BoujeeEnjinia1701/lampnode/cad/drawings/LPN-DWG-001.pdf

CONCEPT, NOT FOR FABRICATION | LampNode · github.com/BoujeeEnjinia1701/lampnode

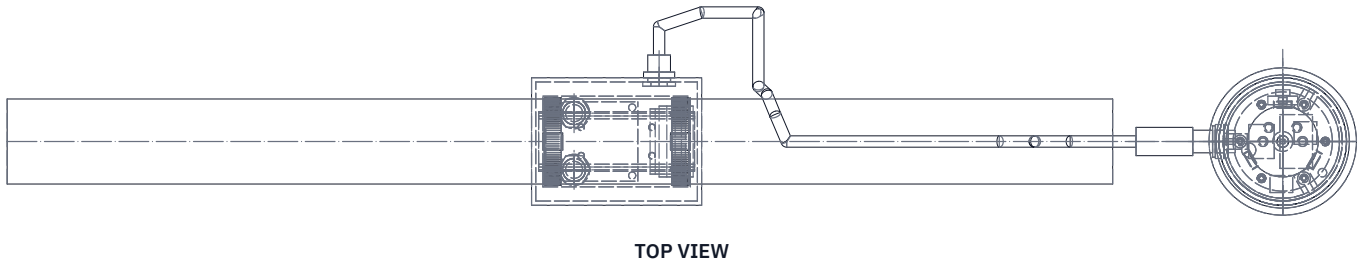
[picture p3: figure]
TOP VIEW
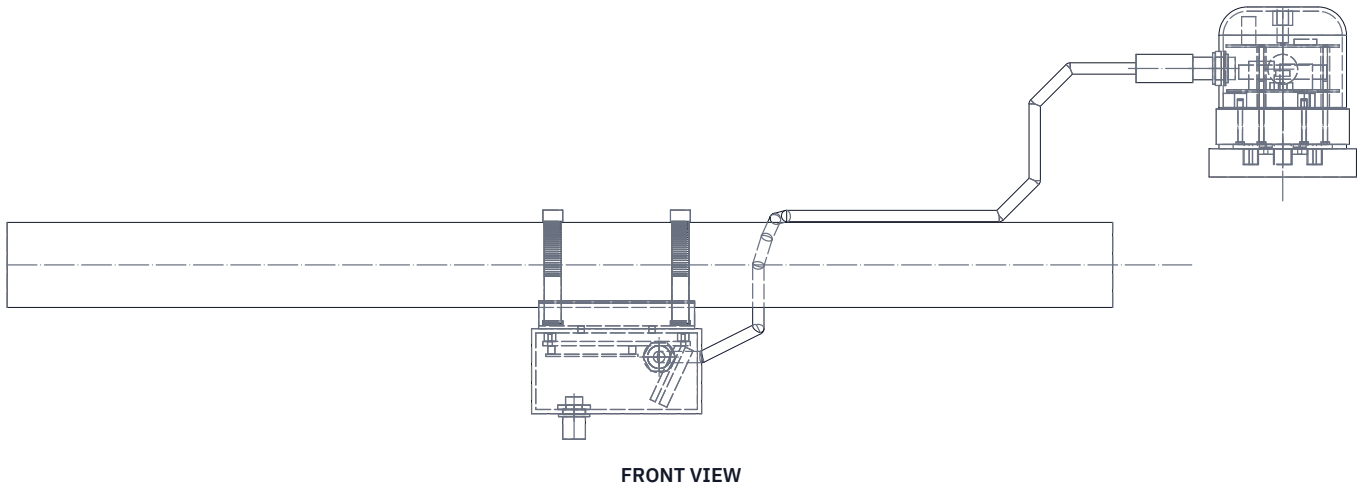
[picture p4: figure]
FRONT VIEW

Scale 1:5; looking at the front (along +Y)

Scale 1:5; looking down (along -Z)

RIGHT VIEW
Scale 1:5; looking at the right side (along -X)

952

147 305

ISOMETRIC VIEW
Not to scale; grey = existing receptacle and arm; seen from the front right and above, about 30 deg elevation

KEY DIMENSIONS AND INTERFACES (MM)
Controller 94 dia. x 111 incl. blades; dome 90 x 72
Base: ANSI C136.41 7-contact twist-lock (representative), 3 power blades, 4 low-voltage contacts, no earth
Sensor head 120 x 90 x 60, center 470 from
receptacle toward the pole; 15 below a 60 dia. arm
Radar tilted 25 deg down, looking along the street
M12 5-pole: dome pad to head, 1 m cable; 2 ports in head lid Band clamps for 50 to 80 arms, pitch 90, through
slots in a folded 2 mm bracket; arm rests on rubber strips
Dome and board stack: 6 x M3 from under the base
Mains 120 to 277 V AC; 0 to 10 V dimming; relay normally closed Ports 12 V SELV, 3 W total; 2.5 W above 50 C inside
US915 radio; port pins 1 12 V, 3 gnd, 2 and 4 RS-485, 5 wake Mass: controller 0.33 kg, head 0.42 kg (LPN-CAL-001) PRELIMINARY, NOT FOR FABRICATION
REV | DESCRIPTION | DATE | BY
P1 | Preliminary GA from cad/src/model.py (LPN-CAL-001) | 2026-09-25 | AC
P2 | Port power note: 2.5 W above 50 C inside (LPN-DDR-002) | 2026-09-25 | AC
P3 | Design for construction: fixings, boards, bracket (LPN-DDR-003) | 2026-09-30 | AC
P4 | Decisions of 2026-10-02: 915 MHz radio band and the M12 port pinout added to the notes | 2026-10-02 | AC
LAMPNODE | github.com/BoujeeEnjinia1701/lampnode

## General arrangement, controller and sensor head

DRAWING NO.
LPN-DWG-001

REV
P4

SHEET
1 of 1

SIZE

## ANSI B

SCALE
1:5

UNITS
mm
PROJECTION | DATE
2026-10-02

DRAWN
Amish Chadha

MATERIAL / NOTES
Dome ASA; base and head box PC; clamps stainless; bracket 2 mm Al. See bom/bom.csv
Licensed CERN-OHL-S-2.0 · Design Molecule Lab · designmolecule.com | Generated from cad/src; do not edit by hand
