BoujeeEnjinia1701/lampnode/cad/drawings/LPN-DWG-106.pdf

### BUILD PLAN SKETCH, PLAN NOT YET BUILT LampNode · github.com/BoujeeEnjinia1701/lampnode

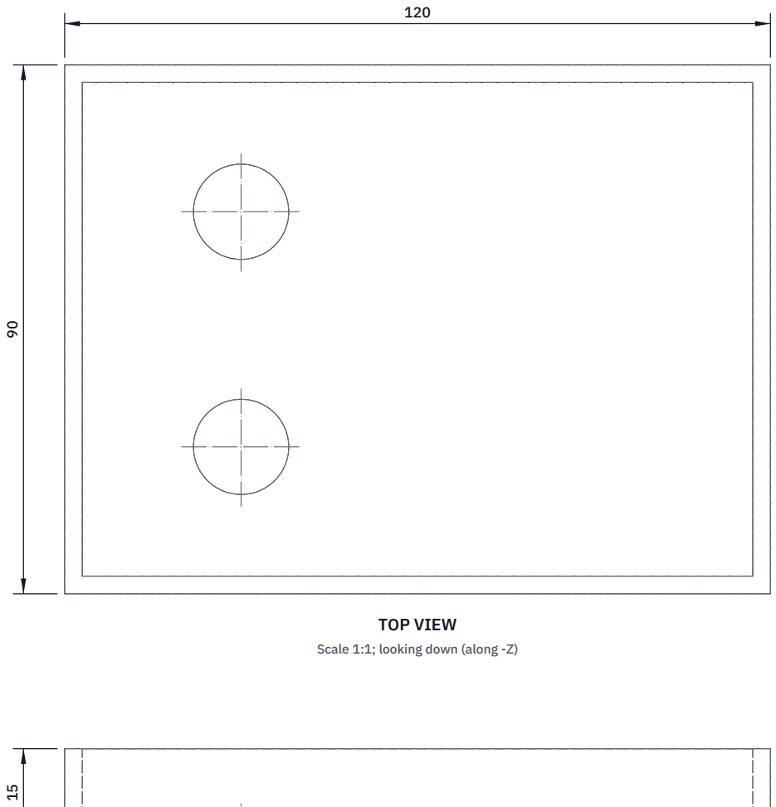
[picture p5: figure]
TOP VIEW; Scale 1:1; looking down (along -Z)

FRONT VIEW
Scale 1:1; looking at the front (along +Y)

RIGHT VIEW
Scale 1:1; looking at the right side (along -X)

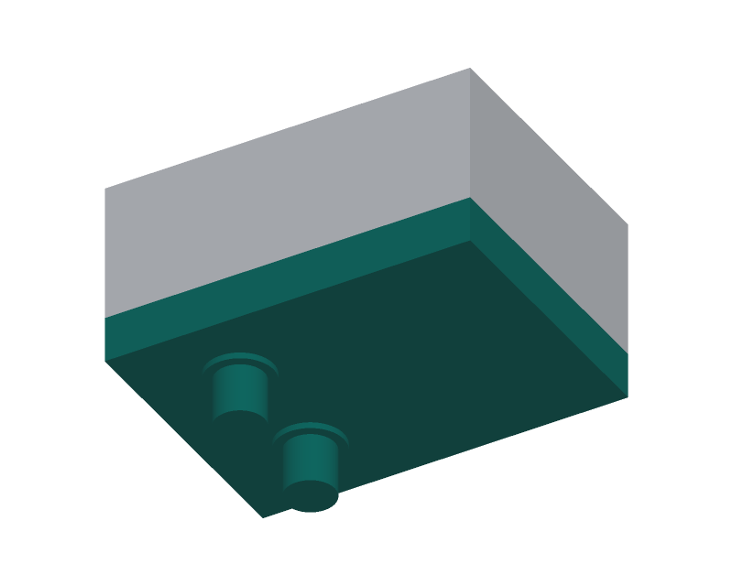
[picture p6: figure]

WHERE IT GOES
This part in colour, its neighbours in grey

HOW TO MAKE IT AND HOW IT FITS
The lid is 15 mm deep and faces the street below.
Two 16.2 mm holes for the M12 expansion ports, 30 mm toward the pole end from the middle, 20 mm each side of the centre line (40 apart). Drill as for the box: tape, 3 mm pilot, step drill, deburr.
Fit each port from outside with its seal, nut inside, maker's torque. Solder a 150 mm lead set to each port and fit a plug-in connector,
so the lid can come off without a soldering iron.
Wire each port to the pinout proposed to FieldNode: pin 1 12 V supply, pin 3 ground, pins 2 and 4 the RS-485 pair, pin 5 wake line.
Check: each port seats flat on its seal; the lid gasket is unbroken.
REV | DESCRIPTION | DATE | BY
P1 | Making sketch for the prototype build plan | 2026-09-30 | AC
P2 | M12 pin numbers added to the notes (decision of 2026-10-02) | 2026-10-02 | AC
LAMPNODE | github.com/BoujeeEnjinia1701/lampnode

## LampNode sensor head lid (bought): drilling sketch

DRAWING NO.
LPN-DWG-106

REV
P2

SHEET
1 of 1

SIZE

## ANSI B

SCALE
1:1

UNITS
mm
PROJECTION | DATE
2026-10-02

DRAWN
Amish Chadha

MATERIAL / NOTES
Lid of the bought IP66 box, polycarbonate
Licensed CERN-OHL-S-2.0 · Design Molecule Lab · designmolecule.com | Generated from cad/src; do not edit by hand
