BoujeeEnjinia1701/lampnode/cad/drawings/LPN-DWG-107.pdf

### BUILD PLAN SKETCH, PLAN NOT YET BUILT LampNode · github.com/BoujeeEnjinia1701/lampnode

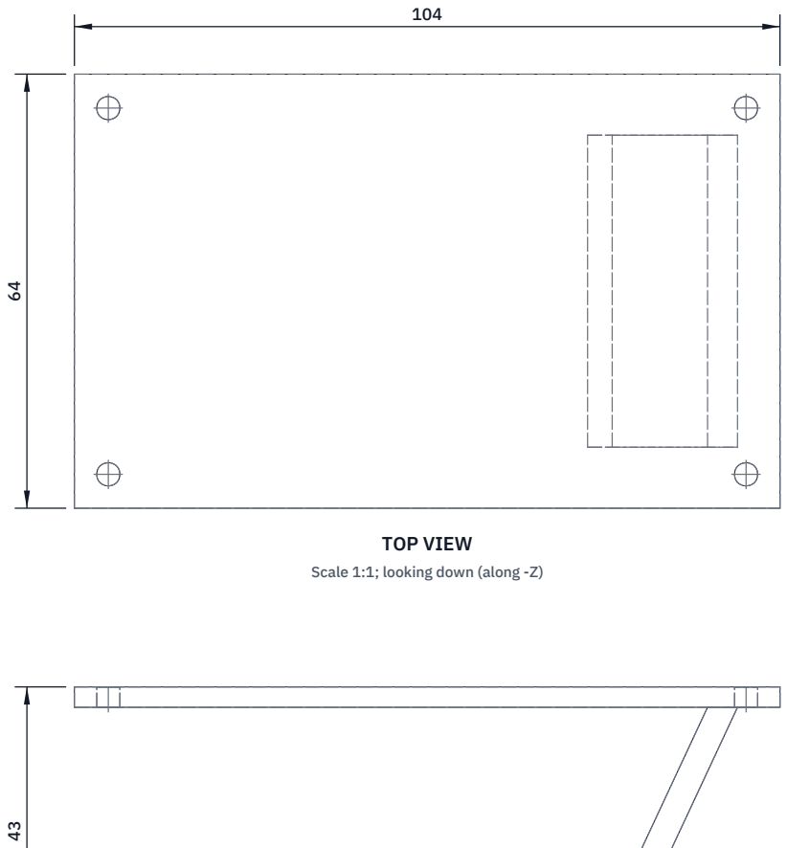
[picture p7: figure]
TOP VIEW; Scale 1:1; looking down (along -Z)

FRONT VIEW
Scale 1:1; looking at the front (along +Y)

RIGHT VIEW
Scale 1:1; looking at the right side (along -X)

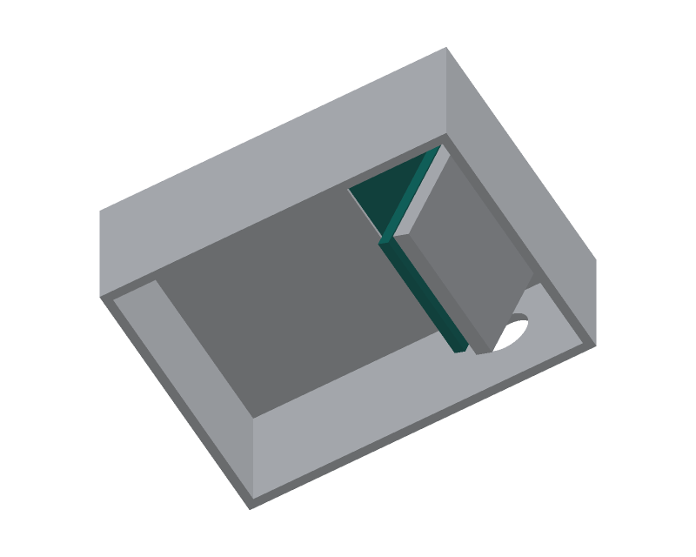
[picture p8: figure]

WHERE IT GOES
This part in colour, its neighbours in grey

HOW TO MAKE IT AND HOW IT FITS
One print: a plate 104 x 64 x 3 mm and a cradle 4 mm thick, 46 mm wide, 44 mm long, hanging below the street end at 25 degrees from upright. Print with the plate flat on the bed and the cradle overhanging.
Four 3.4 mm holes 94 mm apart along and 54 mm apart across, to match the four bosses in the box (measure your box first).
Cradle: two 2.7 mm holes to match the radar module's mounting holes. The module sits 3 mm off the cradle on nylon spacers.
Head board: four M3 standoffs 6 mm long on the underside,
at the board's corner holes, 4 mm in from each edge.
Head board port outputs follow the M12 pinout: pin 1 12 V, pin 3 ground, pins 2 and 4 RS-485, pin 5 wake; the lead plugs are marked 1 to 5.
Fit: four M3 screws into the bosses from below.
Check: the radar face then tips 25 degrees down toward the street.
REV | DESCRIPTION | DATE | BY
P1 | Making sketch for the prototype build plan | 2026-09-30 | AC
P2 | M12 pin numbers added to the notes (decision of 2026-10-02) | 2026-10-02 | AC
LAMPNODE | github.com/BoujeeEnjinia1701/lampnode

## LampNode head internal plate: making sketch

DRAWING NO.
LPN-DWG-107

REV
P2

SHEET
1 of 1

SIZE

## ANSI B

SCALE
1:1

UNITS
mm
PROJECTION | DATE
2026-10-02

DRAWN
Amish Chadha

MATERIAL / NOTES
ASA, 3D printed, 100 % infill
Licensed CERN-OHL-S-2.0 · Design Molecule Lab · designmolecule.com | Generated from cad/src; do not edit by hand
