BoujeeEnjinia1701/lampnode/cad/drawings/LPN-DWG-101.pdf

### BUILD PLAN SKETCH, PLAN NOT YET BUILT LampNode · github.com/BoujeeEnjinia1701/lampnode

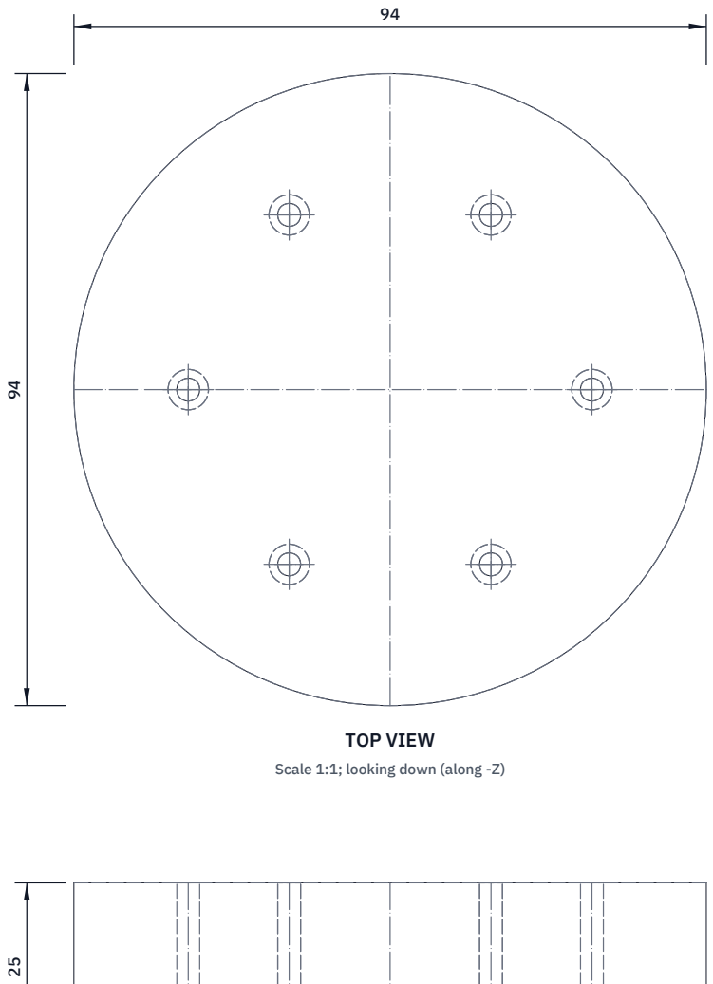
[picture p39: figure]
TOP VIEW; Scale 1:1; looking down (along -Z)

FRONT VIEW
Scale 1:1; looking at the front (along +Y)

RIGHT VIEW
Scale 1:1; looking at the right side (along -X)

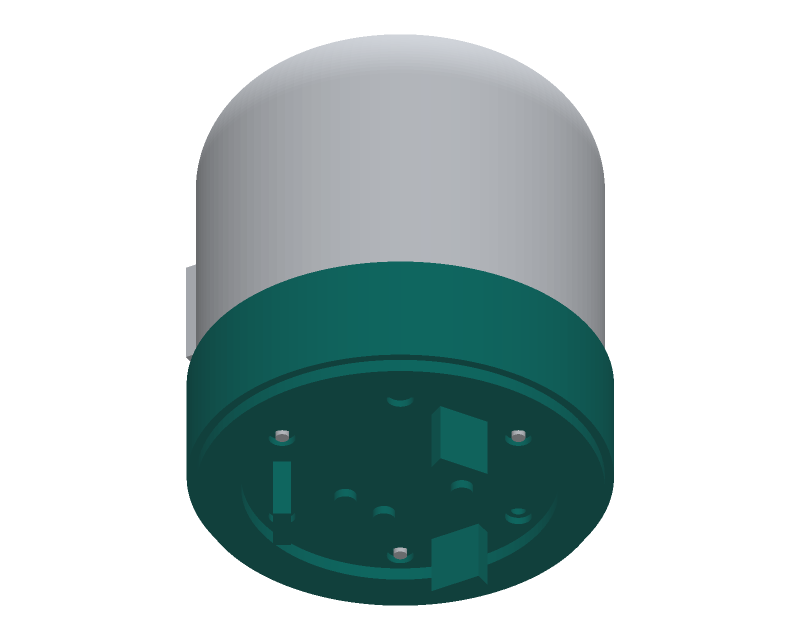
[picture p40: figure]

WHERE IT GOES
This part in colour, its neighbours in grey

HOW TO MAKE IT AND HOW IT FITS
Bought base kit, 94 mm across, 25 mm tall. Drill six holes right through it. All six sit on one 60 mm circle round the centre, between the blades: dome screws at 60, 180 and 300 degrees; stack screws at 0, 120 and 240 degrees, anticlockwise from the street side seen from above.
The base drilling layout picture shows them from below.
Drill 3.4 mm through, with a scrap block under the top face. Countersink each hole from below, 6 mm across, so the screw heads sit flush inside the gasket ring and clear of the contact wells.
Keep the gasket ring (35 to 45 mm radius underneath) untouched. Crimp a 150 mm lead on each blade (1.0 mm2) and each low-voltage contact (0.25 mm2) before anything is fitted on top.
Check: no hole breaks into a blade pocket or the gasket ring.
REV | DESCRIPTION | DATE | BY
P1 | Making sketch for the prototype build plan | 2026-09-30 | AC
LAMPNODE | github.com/BoujeeEnjinia1701/lampnode

## LampNode twist-lock base (bought): drilling sketch

DRAWING NO.
LPN-DWG-101

REV
P1

SHEET
1 of 1

SIZE

## ANSI B

SCALE
1:1

UNITS
mm
PROJECTION | DATE
2026-09-30

DRAWN
Amish Chadha

MATERIAL / NOTES
Bought ANSI C136.41 7-contact base kit, polycarbonate
Licensed CERN-OHL-S-2.0 · Design Molecule Lab · designmolecule.com | Generated from cad/src; do not edit by hand
