BoujeeEnjinia1701/lampnode/cad/drawings/LPN-DWG-102.pdf

### BUILD PLAN SKETCH, PLAN NOT YET BUILT LampNode · github.com/BoujeeEnjinia1701/lampnode

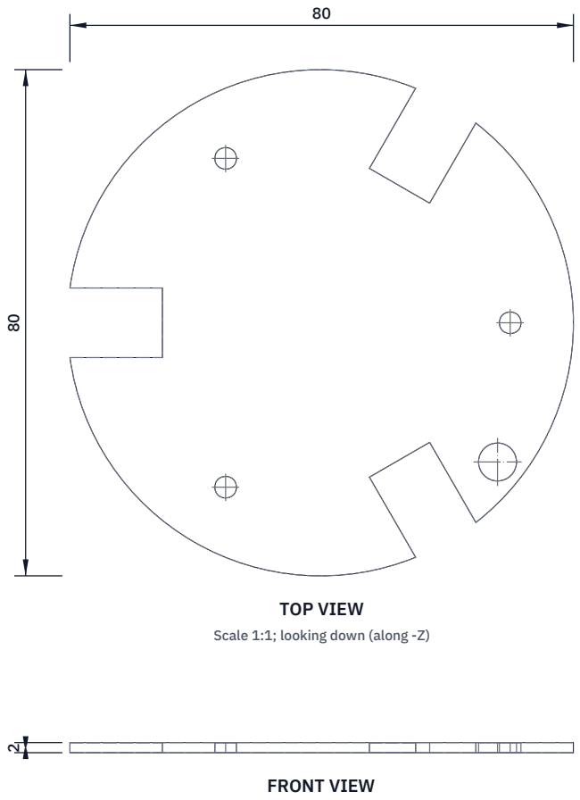
[picture p41: figure]
FRONT VIEW; TOP VIEW; Scale 1:1; looking down (along -Z)

Scale 1:1; looking at the front (along +Y)

RIGHT VIEW
Scale 1:1; looking at the right side (along -X)

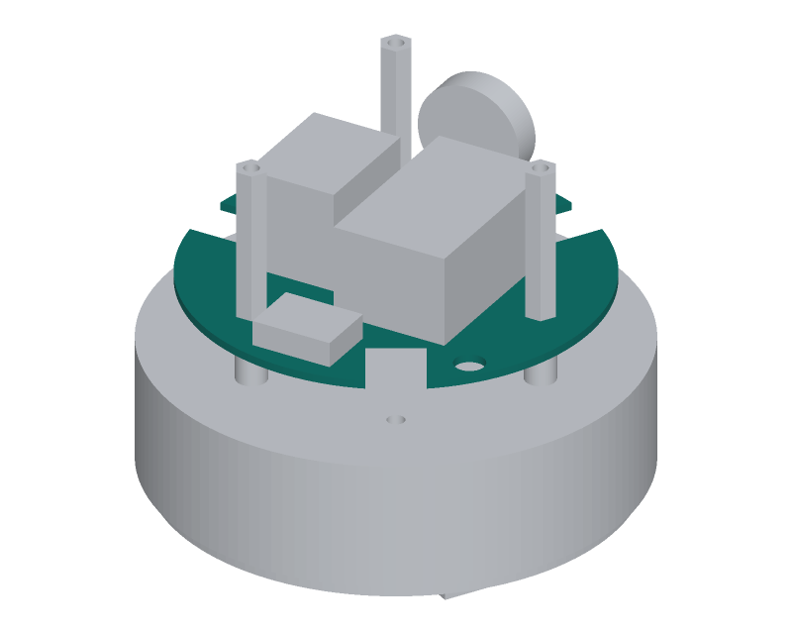
[picture p42: figure]

WHERE IT GOES
This part in colour, its neighbours in grey

HOW TO MAKE IT AND HOW IT FITS
Cut an 80 mm disc from plated-hole prototype board (2.54 mm grid): scribe the circle, cut outside it with a coping saw, file to the line.
Three stack holes 3.4 mm on a 60 mm circle at 0, 120 and 240 degrees. Three notches 11 mm wide, from 25 mm radius out to the edge, at 60, 180 and 300 degrees: the dome bosses pass up through them.
Parts, from the mains board layout picture: supply 23 x 38 mm on the centre; relay on the pole side; varistor and thermal fuse at the left
edge and metering module at the right edge, seen from the pole.
6 mm hole at 28 mm toward the street, 22 mm right: low-voltage leads. Keep 6 mm of bare board between mains tracks and the 12 V side. Fit a 3-way mains terminal block and a 6-way harness header.
Fit: sits on three 12 mm spacers; standoffs screw on top.
Check: flat; the dome bosses pass the notches freely.
REV | DESCRIPTION | DATE | BY
P1 | Making sketch for the prototype build plan | 2026-09-30 | AC
LAMPNODE | github.com/BoujeeEnjinia1701/lampnode

## LampNode mains board: making sketch

DRAWING NO.
LPN-DWG-102

REV
P1

SHEET
1 of 1

SIZE

## ANSI B

SCALE
1:1

UNITS
mm
PROJECTION | DATE
2026-09-30

DRAWN
Amish Chadha

MATERIAL / NOTES
Plated-hole FR4 prototype board 1.6 mm
Licensed CERN-OHL-S-2.0 · Design Molecule Lab · designmolecule.com | Generated from cad/src; do not edit by hand
