BoujeeEnjinia1701/lampnode/cad/drawings/LPN-DWG-103.pdf

### BUILD PLAN SKETCH, PLAN NOT YET BUILT LampNode · github.com/BoujeeEnjinia1701/lampnode

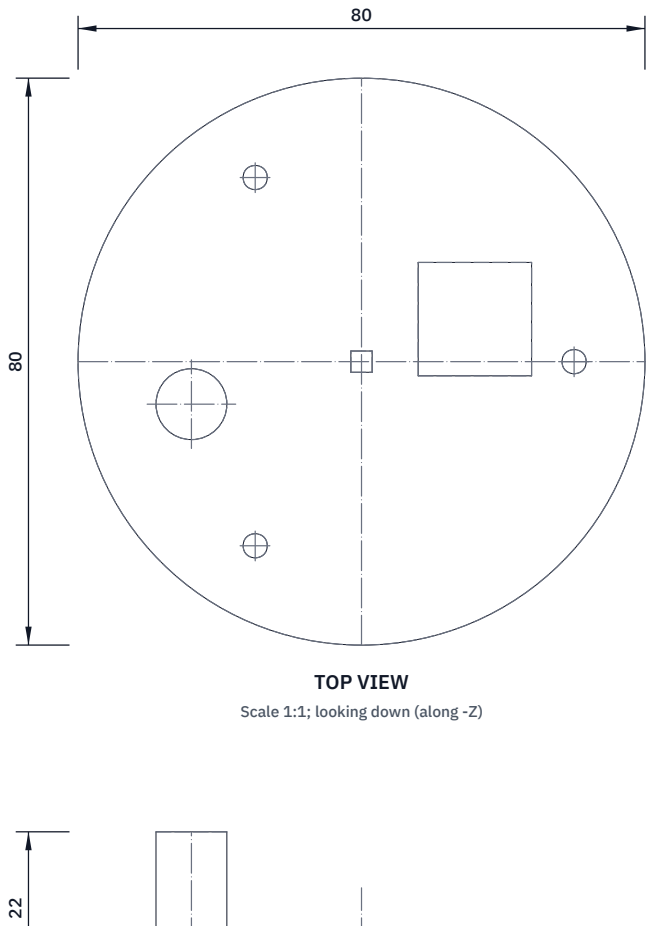
[picture p43: figure]
TOP VIEW; Scale 1:1; looking down (along -Z)

FRONT VIEW
Scale 1:1; looking at the front (along +Y)

RIGHT VIEW
Scale 1:1; looking at the right side (along -X)

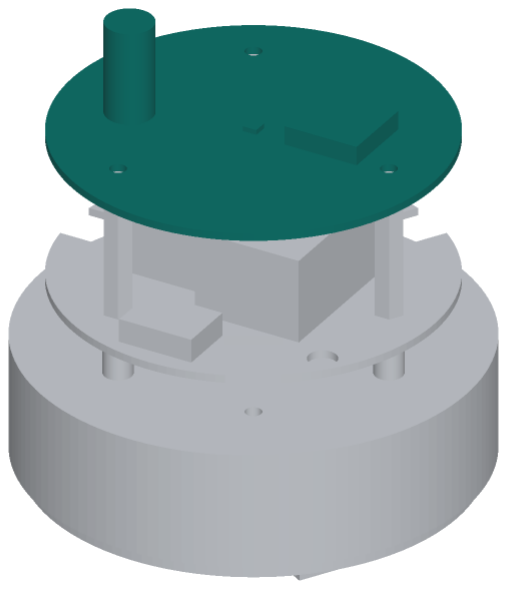
[picture p44: figure]

WHERE IT GOES
This part in colour, its neighbours in grey

HOW TO MAKE IT AND HOW IT FITS
Cut an 80 mm disc as for the mains board; no notches.
Three holes 3.4 mm on a 60 mm circle at 0, 120 and 240 degrees. Light sensor at the exact centre, on the top face; the light pipe
ends 0.5 mm above it once the dome is on.
Radio module breakout 16 x 16 mm on the street side, its u.FL socket toward the right edge (seen from the pole) for the antenna lead. Supercapacitor 10 mm across, 20 mm tall, standing 24 mm toward the pole and 6 mm to the right of the centre, clear of the screw heads.
Clock, accelerometer, 0 to 10 V stage and coil drive on the rest.
Fit: three M3 x 6 screws into the standoffs, top of board 70.2 mm
above the underside of the base.
Check: nothing on the top face stands taller than 22 mm.
REV | DESCRIPTION | DATE | BY
P1 | Making sketch for the prototype build plan | 2026-09-30 | AC
LAMPNODE | github.com/BoujeeEnjinia1701/lampnode

## LampNode controller board: making sketch

DRAWING NO.
LPN-DWG-103

REV
P1

SHEET
1 of 1

SIZE

## ANSI B

SCALE
1:1

UNITS
mm
PROJECTION | DATE
2026-09-30

DRAWN
Amish Chadha

MATERIAL / NOTES
Plated-hole FR4 prototype board 1.6 mm
Licensed CERN-OHL-S-2.0 · Design Molecule Lab · designmolecule.com | Generated from cad/src; do not edit by hand
