BoujeeEnjinia1701/lampnode/cad/drawings/LPN-DWG-104.pdf

### BUILD PLAN SKETCH, PLAN NOT YET BUILT LampNode · github.com/BoujeeEnjinia1701/lampnode

FRONT VIEW
Scale 1:2; looking at the front (along +Y)

TOP VIEW
Scale 1:2; looking down (along -Z)

RIGHT VIEW
Scale 1:2; looking at the right side (along -X)

92

90 71

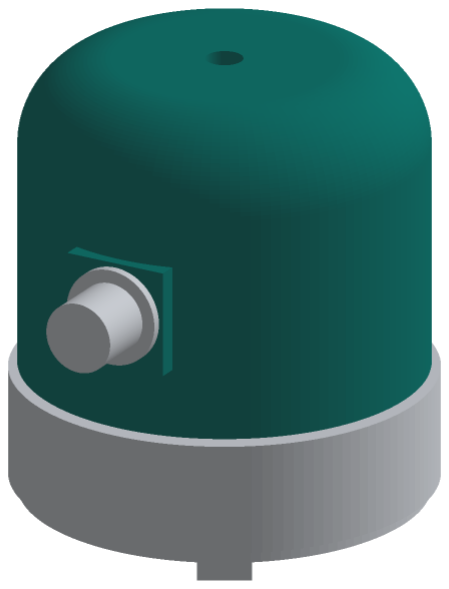
[picture p45: figure]

WHERE IT GOES
This part in colour, its neighbours in grey

HOW TO MAKE IT AND HOW IT FITS
Print upside down on its top, in ASA in an enclosed printer.
Shell 90 mm across, 71 mm tall, 3 mm wall, 20 mm round top edge. Three bosses 9 mm across, 10 mm tall, inside the foot on a 60 mm circle at 60, 180 and 300 degrees, each tied to the wall by a rib. Press an M3 brass heat-set insert into each boss with a soldering iron. Flat pad on the pole side (180 degrees): 24 x 24 mm, 6 mm thick, face 0.5 mm outside the base edge, centre 27.6 mm above the dome foot. 16.2 mm hole through it for the M12 socket.
Light pipe hole 8.2 mm at the top centre, with a 10 mm sleeve inside. Gasket: cut a ring 90 mm outside, 84 mm inside from 1 mm EPDM sheet. Fit: foot on the gasket; three M3 x 30 screws from under the base. Check: the foot sits flat on the base all round, no light under it.
REV | DESCRIPTION | DATE | BY
P1 | Making sketch for the prototype build plan | 2026-09-30 | AC
LAMPNODE | github.com/BoujeeEnjinia1701/lampnode

## LampNode dome: making sketch

DRAWING NO.
LPN-DWG-104

REV
P1

SHEET
1 of 1

SIZE

## ANSI B

SCALE
1:2

UNITS
mm
PROJECTION | DATE
2026-09-30

DRAWN
Amish Chadha

MATERIAL / NOTES
ASA, 3D printed, 4 walls, 40 % infill
Licensed CERN-OHL-S-2.0 · Design Molecule Lab · designmolecule.com | Generated from cad/src; do not edit by hand
