BoujeeEnjinia1701/lampnode/cad/drawings/LPN-DWG-105.pdf

### BUILD PLAN SKETCH, PLAN NOT YET BUILT LampNode · github.com/BoujeeEnjinia1701/lampnode

FRONT VIEW
Scale 1:2; looking at the front (along +Y)

TOP VIEW
Scale 1:2; looking down (along -Z)

RIGHT VIEW
Scale 1:2; looking at the right side (along -X)

120

90 45

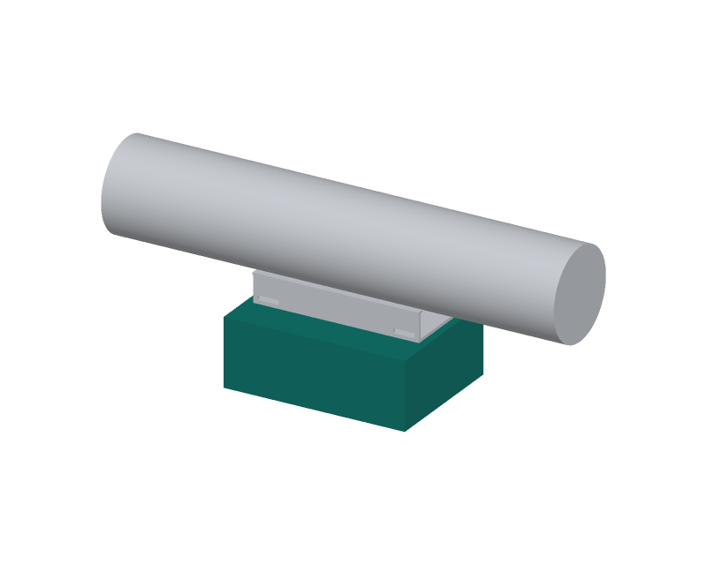
[picture p46: figure]

WHERE IT GOES
This part in colour, its neighbours in grey

HOW TO MAKE IT AND HOW IT FITS
Bought box; its base faces up and its 15 mm lid faces down.
The end wall facing the street end of the arm is the radar window: never drill it, paint it or put a label on it.
Top face: four 4.5 mm holes for the bracket screws, 25 mm each side of the middle along the box and 10 mm each side across it.
Left side wall, seen from the pole: one 16.2 mm hole for the cable gland, 30 mm toward the street end from the middle, 20 mm below the top. Tape the faces, pilot drill 3 mm slowly, open out with a step drill.
No solvents: polycarbonate crazes. Deburr inside and out.
Check the four inside bosses are 94 x 54 mm apart; if not, move the internal plate holes to suit.
REV | DESCRIPTION | DATE | BY
P1 | Making sketch for the prototype build plan | 2026-09-30 | AC
LAMPNODE | github.com/BoujeeEnjinia1701/lampnode

## LampNode sensor head box (bought): drilling sketch

DRAWING NO.
LPN-DWG-105

REV
P1

SHEET
1 of 1

SIZE

## ANSI B

SCALE
1:2

UNITS
mm
PROJECTION | DATE
2026-09-30

DRAWN
Amish Chadha

MATERIAL / NOTES
Bought IP66 polycarbonate box 120 x 90 x 60 mm
Licensed CERN-OHL-S-2.0 · Design Molecule Lab · designmolecule.com | Generated from cad/src; do not edit by hand
