BoujeeEnjinia1701/lampnode/cad/drawings/LPN-DWG-108.pdf

### BUILD PLAN SKETCH, PLAN NOT YET BUILT LampNode · github.com/BoujeeEnjinia1701/lampnode

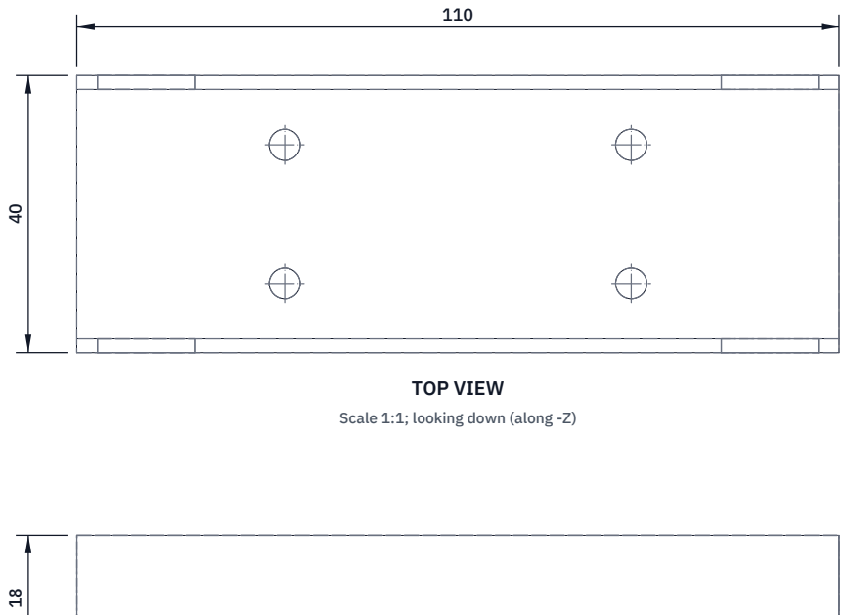
[picture p47: figure]
TOP VIEW; Scale 1:1; looking down (along -Z)

FRONT VIEW
Scale 1:1; looking at the front (along +Y)

RIGHT VIEW
Scale 1:1; looking at the right side (along -X)

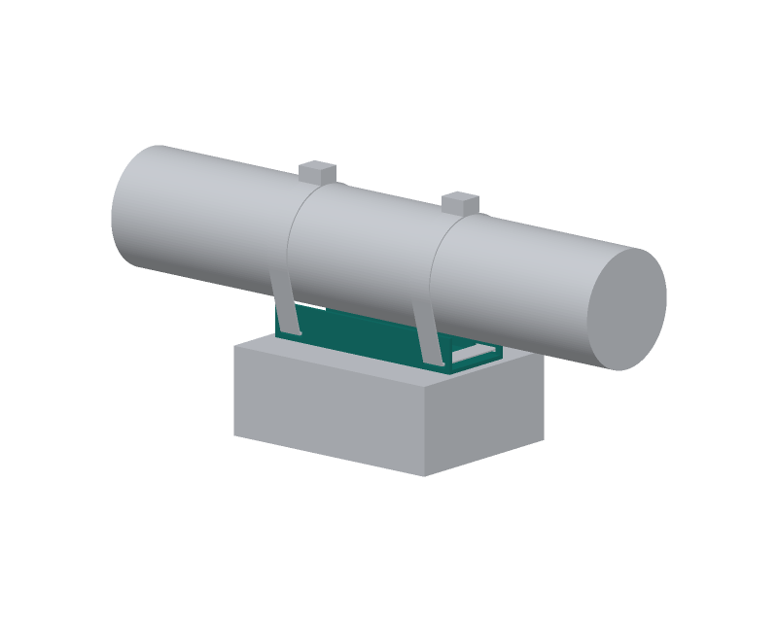
[picture p48: figure]

WHERE IT GOES
This part in colour, its neighbours in grey

HOW TO MAKE IT AND HOW IT FITS
Blank 110 x 70 mm from 2 mm sheet. Mark two fold lines 17 mm in from the long edges and fold both flanges up 90 degrees in a bending brake.
Folded: web 40 mm across outside; flanges 18 mm tall from the underside of the web (file the tops level if they come out taller).
Web: four 4.5 mm holes, 25 mm each side of the middle along the bracket and 10 mm each side of the centre line across it.
Band slots after folding: one through each flange, 14 x 3 mm, centred 45 mm each side of the middle, just above the web: drill 3 mm at each end through the bend and file between. Deburr every edge.
Rubber strips: 110 x 5 mm, 1.5 mm EPDM, glued along each flange top, overhanging the flange 2 mm inside and 1 mm outside.
Check: the arm rests on both strips, not on the metal.
REV | DESCRIPTION | DATE | BY
P1 | Making sketch for the prototype build plan | 2026-09-30 | AC
LAMPNODE | github.com/BoujeeEnjinia1701/lampnode

## LampNode arm bracket: making sketch

DRAWING NO.
LPN-DWG-108

REV
P1

SHEET
1 of 1

SIZE

## ANSI B

SCALE
1:1

UNITS
mm
PROJECTION | DATE
2026-09-30

DRAWN
Amish Chadha

MATERIAL / NOTES
Aluminium sheet 2 mm, 5052 class
Licensed CERN-OHL-S-2.0 · Design Molecule Lab · designmolecule.com | Generated from cad/src; do not edit by hand
