BoujeeEnjinia1701/lampnode/cad/drawings/LPN-DWG-001.png

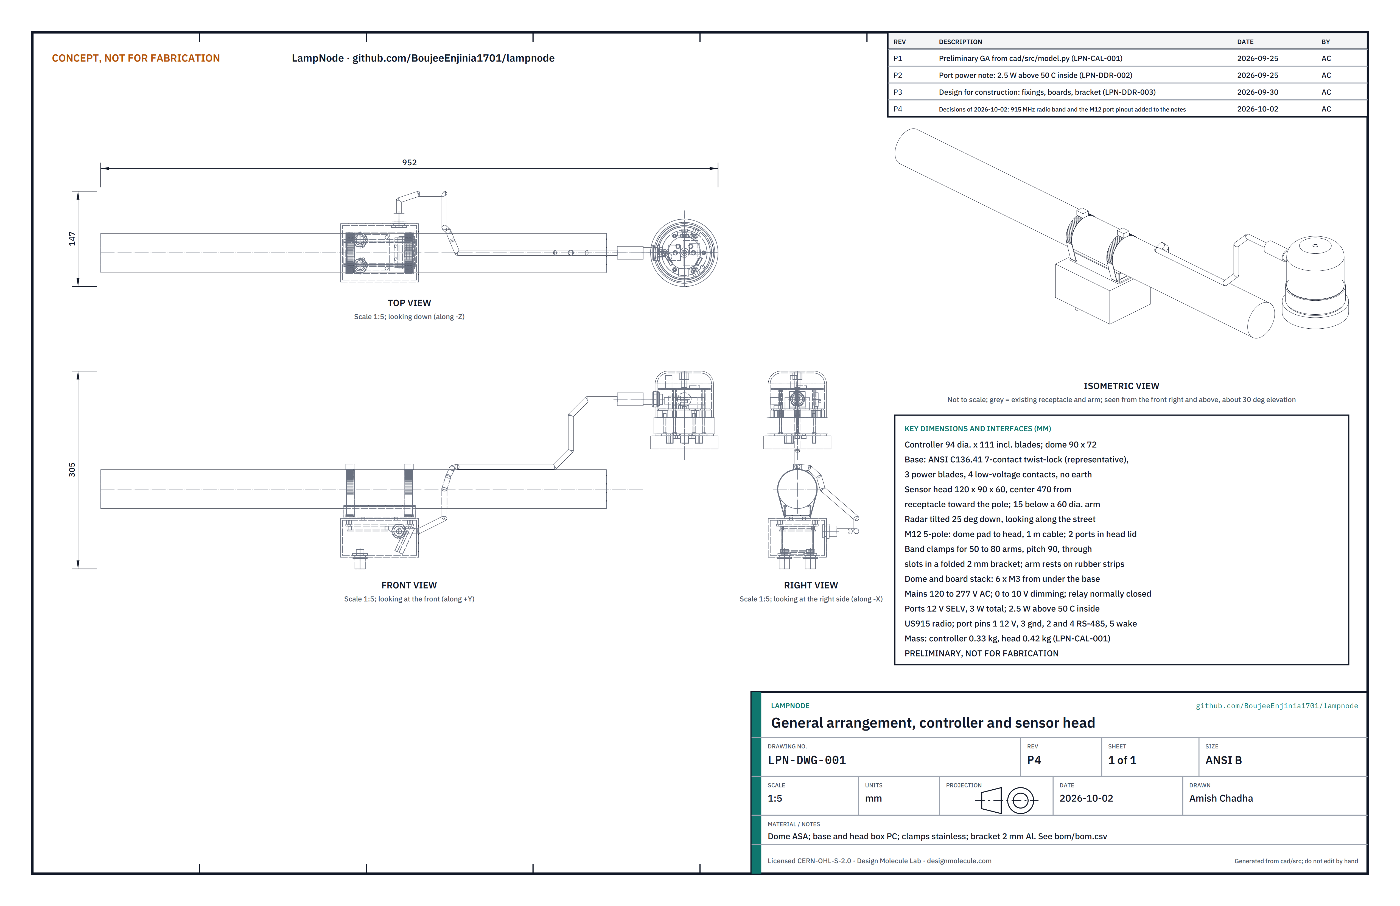
cad/drawings/LPN-DWG-001.png
