BoujeeEnjinia1701/lampnode/media/card.png

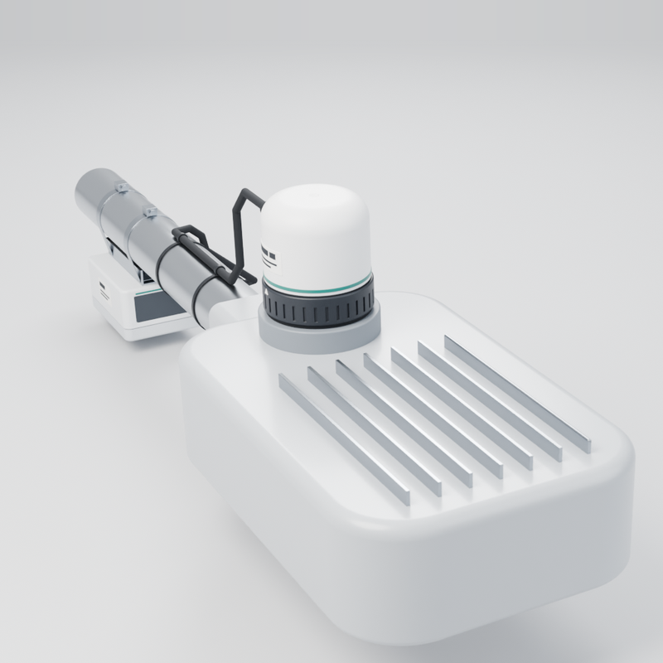
media/card.png
