BoujeeEnjinia1701/lampnode/media/cutaway.png

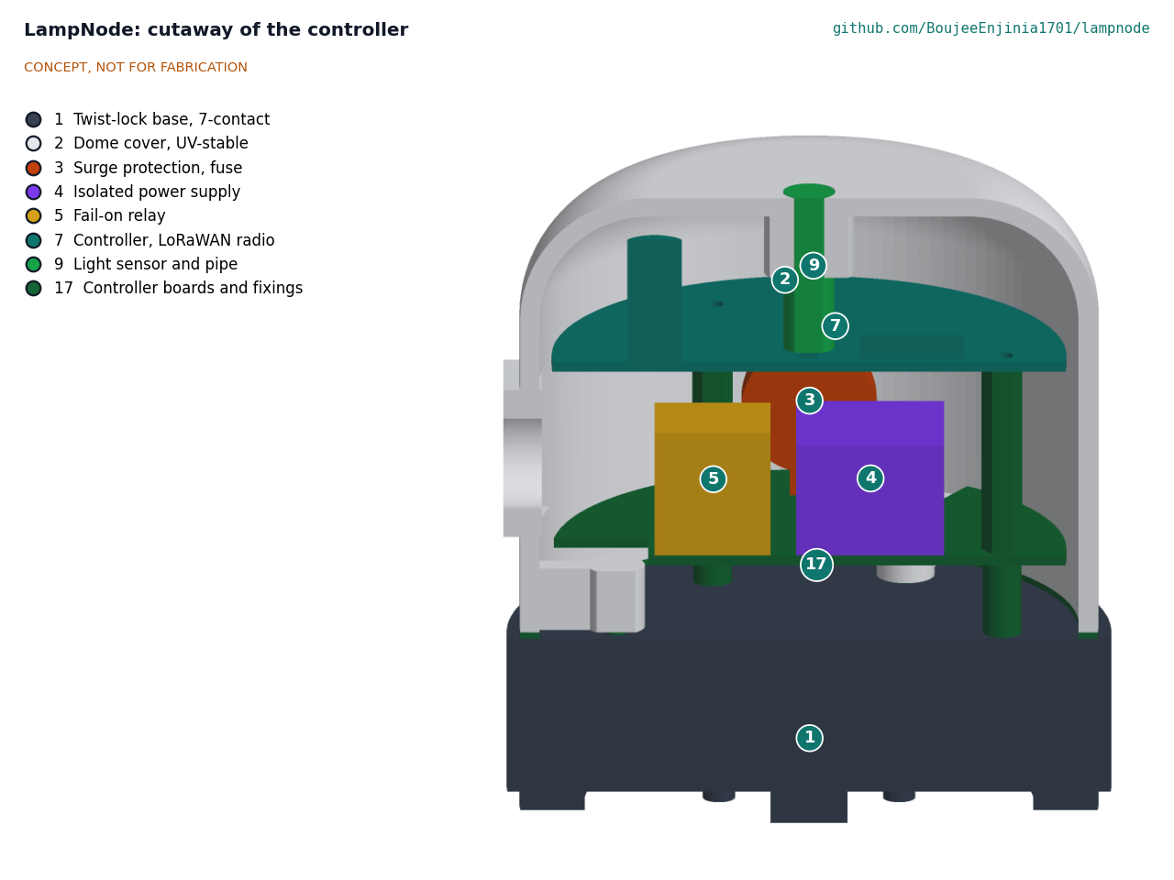
media/cutaway.png
