BoujeeEnjinia1701/lampnode/media/exploded.png

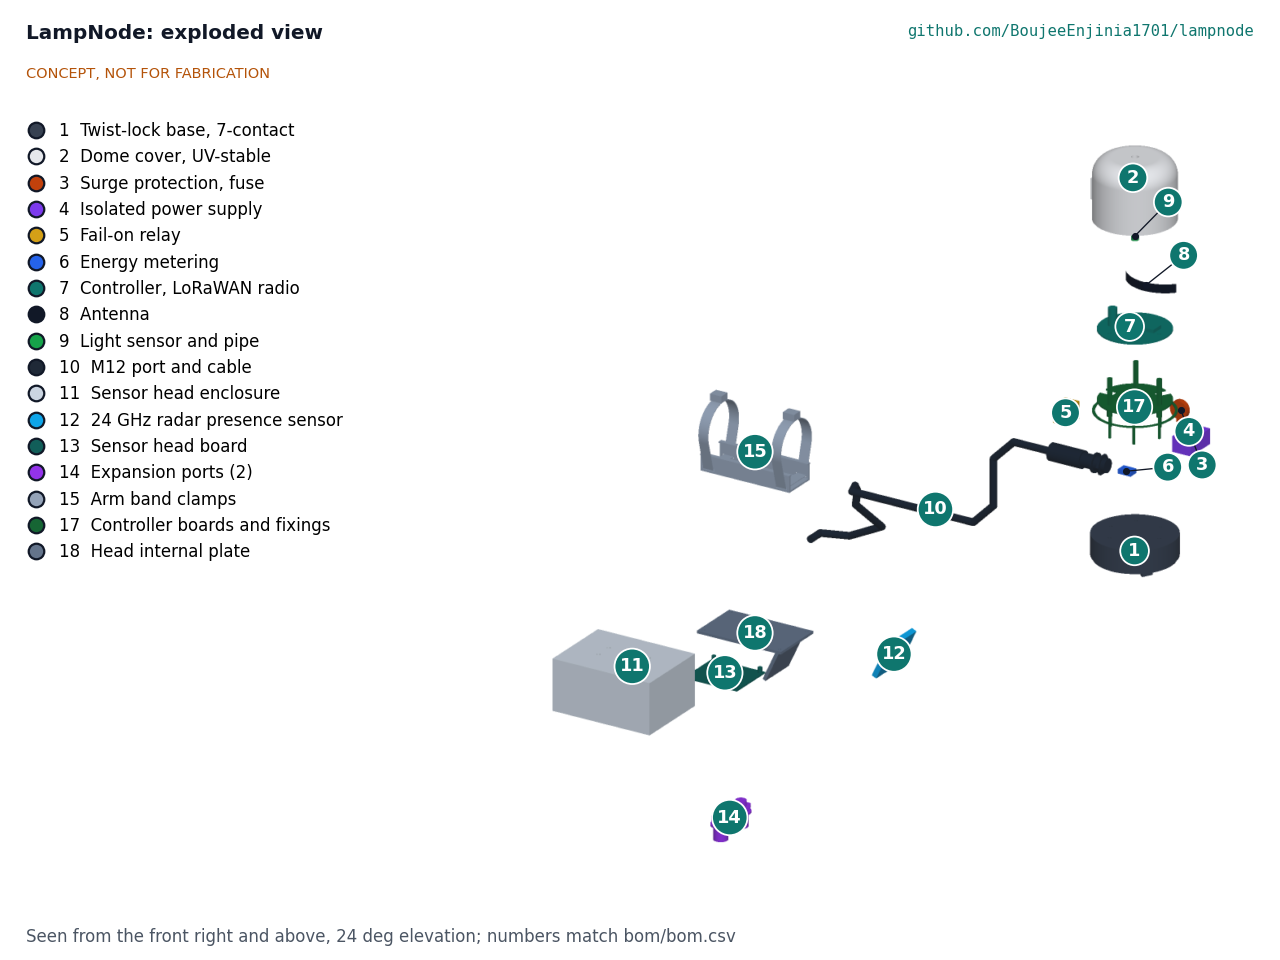
media/exploded.png
