BoujeeEnjinia1701/lampnode/media/flow.png

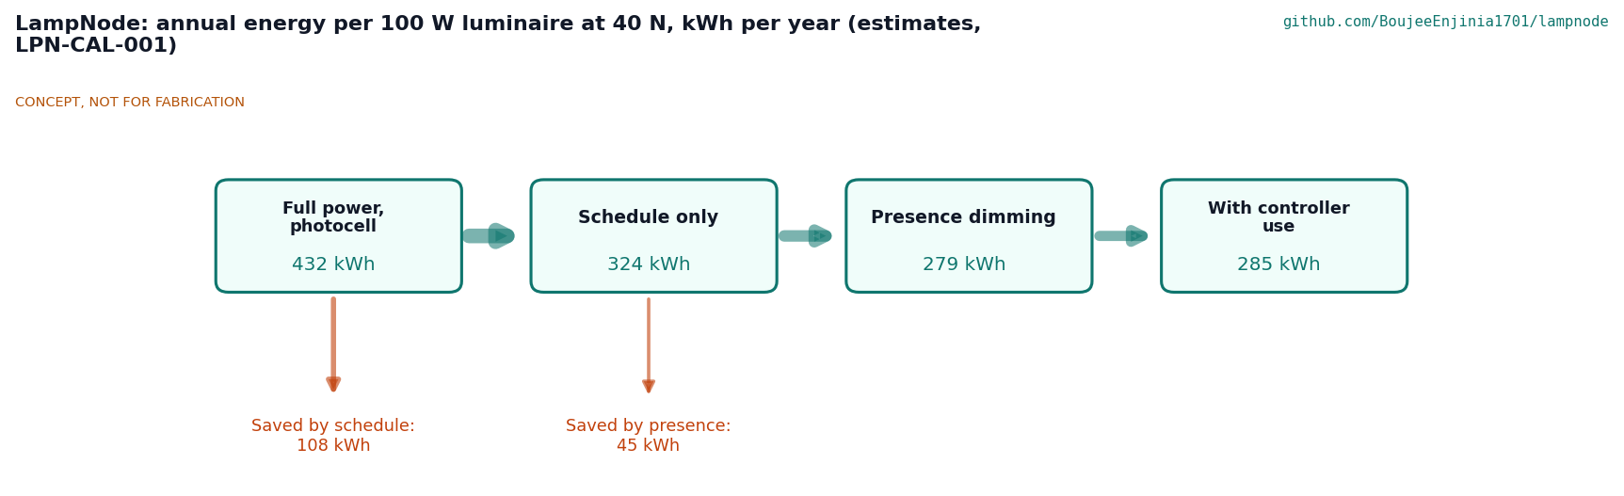
media/flow.png
