BoujeeEnjinia1701/lampnode/media/hero.png

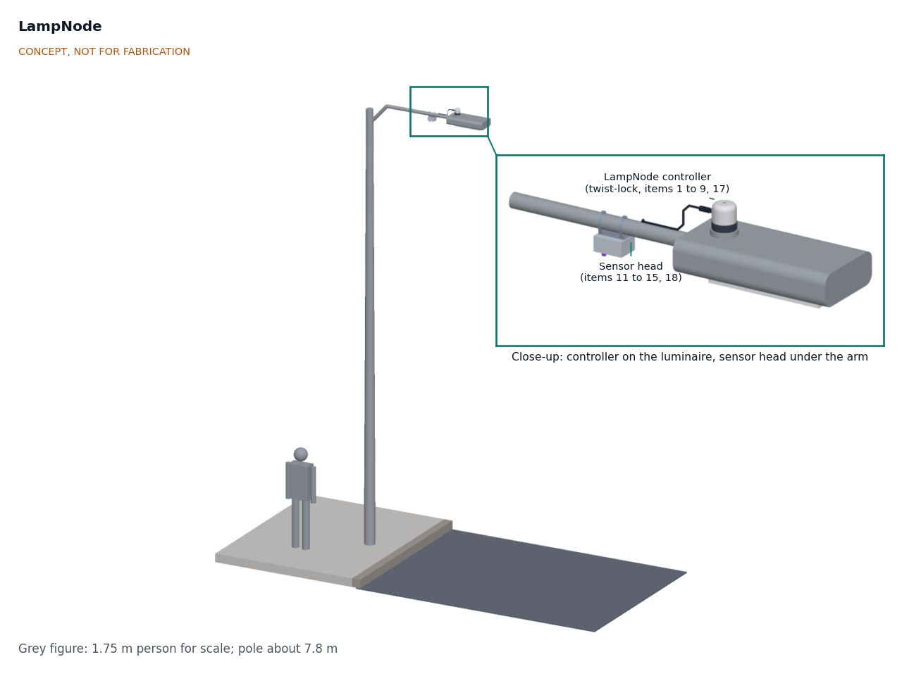
media/hero.png
