BoujeeEnjinia1701/lampnode/media/render-detail.png

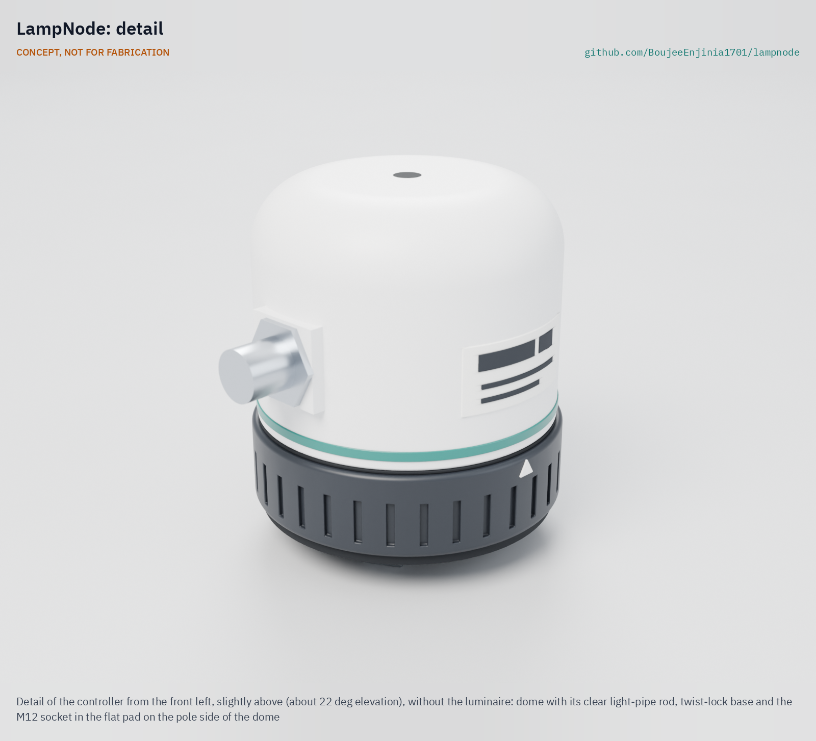
media/render-detail.png
