BoujeeEnjinia1701/lampnode/media/render-exploded.png

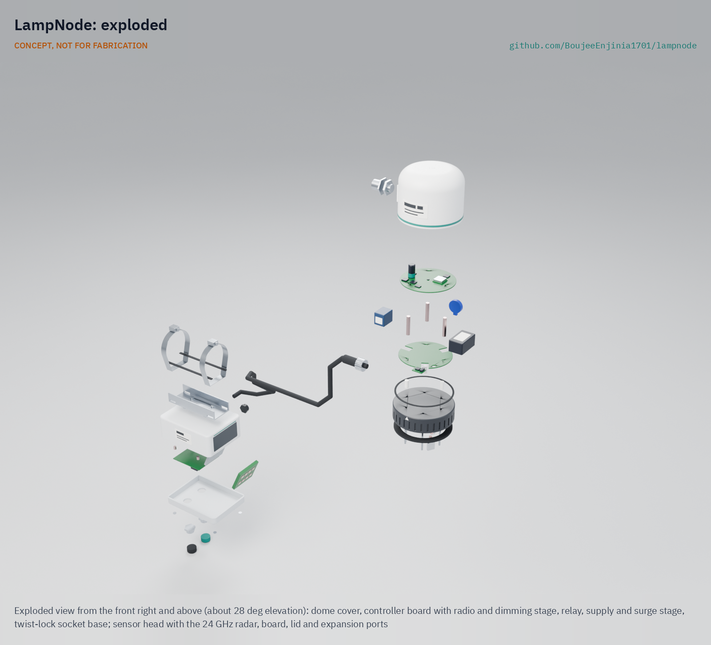
media/render-exploded.png
