BoujeeEnjinia1701/lampnode/media/social-preview.png

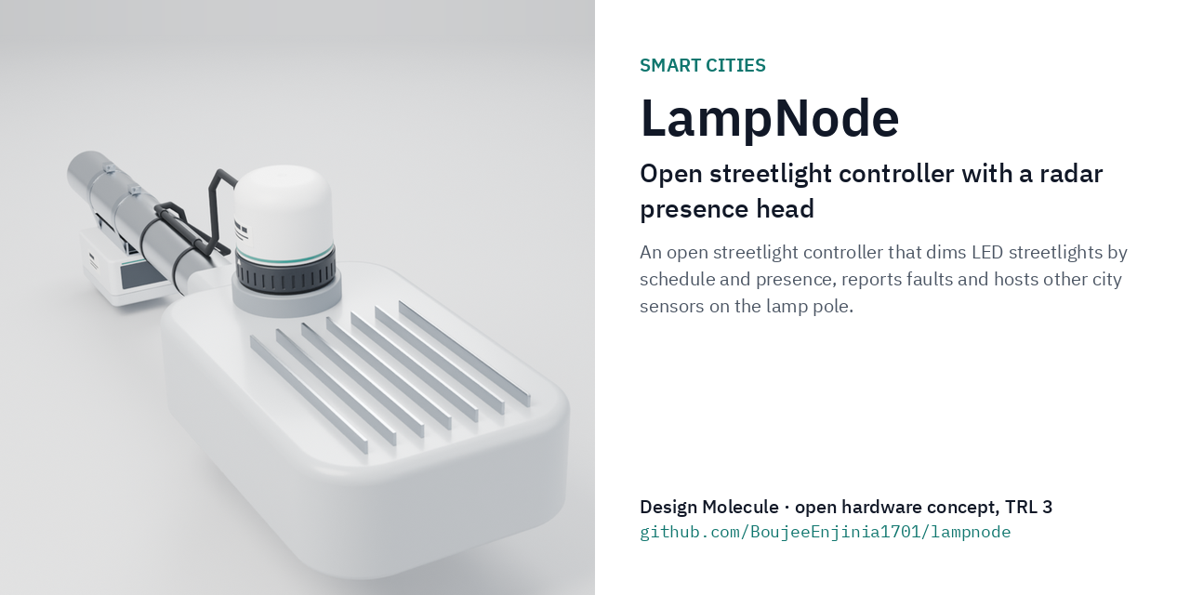
media/social-preview.png
